bharrisau/operon/firmware/include/operon.h

#ifndef __OPERON_H
#define __OPERON_H

#ifdef __cplusplus
 extern "C" {
#if 0
}
#endif
#endif

#include <MKL25Z.h>

/* defines for pin locations of peripherals
   includes for all the peripherals used
   */



#ifdef __cplusplus
}
#endif

#endif
